Pichitek/LVPM/sim/alert_filter.asc

C1: cap; 320n
C2: cap; 320n
R1: res; 1k
R2: res; 1k
U1: UniversalOpAmp
V1: voltage; PULSE(0 3.3 0 1n 1n 25u 125u); AC 1
V2: voltage; 3.3
Named nets: 0, +3V3
.tran 5m
80%  100u 125u
50%   62.5u 125u
20%   25u   125u
