Pichitek/LVPM/sim/voltage_sense_w_dcdc.asc

C1: cap; 100n
C2: cap; 1µ
C3: cap; 1n
C4: cap; 100n
C5: cap; 100n
C6: cap; 1n
C7: cap; 10n
C8: cap; 1n
C9: cap; 1µ
C10: cap; 1n
C11: cap; 1n
CF: cap; 10n
R1: res; 1Meg
R2: res; 1Meg
R3: res; 330
R4: res; 47k
RF1: res; 10
RF2: res; 10
U1: AMC3330
V1: voltage; 600
V2: voltage; 3.3
Named nets: 0, +3.3, outp, outn
.tran 15m
